a10kiloham/NicePillzViewZMK/boards/shields/nicepillz/custom_status_screen.c

/*
 * Nice Pillz nice!view status screen - ZMK glue.
 *
 * Portrait layout, header pins at the bottom:
 *
 *      [=====]  87%     battery gauge + percent, or "Charging" when on USB
 *      [ 63 /\/\_ ]    words per minute: history graph, one sample per 5 s
 *      (BT) 1 ok        output: bluetooth logo + profile numeral, or a USB symbol
 *   (1)(2)(3)(4)(5)     active layer
 *     [Caps Lock]       HID lock indicators
 *    Ctrl Alt Shift     held modifier keys, and the Program key
 *      Win Prgm
 *
 * Everything is drawn upright into a 68x160 canvas by view_draw.c, then
 * rotated into the panel's native 160x68 buffer. All LVGL work happens on
 * the ZMK display work queue.
 *
 * With CONFIG_NICEPILLZ_DISPLAY_LANDSCAPE the same elements are laid out for
 * 160x68, drawn into the panel buffer and turned 180 degrees (header pins on the right).
 *
 * SPDX-License-Identifier: MIT
 */
#include <zephyr/kernel.h>
#include <string.h>
#include <lvgl.h>

#include <zmk/display.h>
#include <zmk/display/status_screen.h>
#include <zmk/event_manager.h>
#include <zmk/events/battery_state_changed.h>
#include <zmk/events/usb_conn_state_changed.h>
#include <zmk/events/ble_active_profile_changed.h>
#include <zmk/events/endpoint_changed.h>
#include <zmk/events/layer_state_changed.h>
#include <zmk/events/hid_indicators_changed.h>
#include <zmk/events/keycode_state_changed.h>
#include <dt-bindings/zmk/hid_usage.h>
#include <dt-bindings/zmk/hid_usage_pages.h>
#include <zmk/hid.h>
#include <zmk/battery.h>
#include <zmk/usb.h>
#include <zmk/ble.h>
#include <zmk/endpoints.h>
#include <zmk/keymap.h>
#include <zmk/hid_indicators.h>
#include <zmk/wpm.h>

#include "view_draw.h"

/* HID boot keyboard output report bits */
#define HID_LED_NUM_LOCK BIT(0)
#define HID_LED_CAPS_LOCK BIT(1)
#define HID_LED_SCROLL_LOCK BIT(2)

#if !IS_ENABLED(CONFIG_NICEPILLZ_DISPLAY_LANDSCAPE)
static lv_color_t upright_buf[NPV_W * NPV_H];
static lv_obj_t *upright_canvas;
#endif
static lv_color_t panel_buf[NPV_PANEL_W * NPV_PANEL_H];
static lv_obj_t *panel_canvas;

static struct npv_state state;
static K_MUTEX_DEFINE(state_lock);
static int64_t last_wpm_update;

/* Modifier keys currently down, one bit per HID usage Left Ctrl (0xE0) .. Right GUI (0xE7).
 * ZMK never raises zmk_modifiers_state_changed, so this is tracked from the keycode events. */
static uint8_t held_mod_keys;

static uint8_t mod_bits(uint8_t keys) {
    uint8_t m = 0;
    if (keys & 0x11) {
        m |= NPV_MOD_CTRL;
    }
    if (keys & 0x22) {
        m |= NPV_MOD_SHIFT;
    }
    if (keys & 0x44) {
        m |= NPV_MOD_ALT;
    }
    if (keys & 0x88) {
        m |= NPV_MOD_GUI;
    }
    return m;
}

static void capture_zmk_state(struct npv_state *s) {
    s->battery = zmk_battery_state_of_charge();
    s->charging = zmk_usb_is_powered();

    struct zmk_endpoint_instance ep = zmk_endpoints_selected();
    s->transport = (ep.transport == ZMK_TRANSPORT_USB) ? NPV_TRANSPORT_USB : NPV_TRANSPORT_BLE;
    s->ble_profile = zmk_ble_active_profile_index();
    s->ble_connected = zmk_ble_active_profile_is_connected();
    s->ble_open = zmk_ble_active_profile_is_open();

    s->layer = zmk_keymap_highest_layer_active();

    zmk_hid_indicators_t ind = zmk_hid_indicators_get_current_profile();
    s->num_lock = ind & HID_LED_NUM_LOCK;
    s->caps_lock = ind & HID_LED_CAPS_LOCK;
    s->scroll_lock = ind & HID_LED_SCROLL_LOCK;

    s->mods = mod_bits(held_mod_keys);
    if (zmk_keymap_layer_active(CONFIG_NICEPILLZ_PROGRAM_LAYER)) {
        s->mods |= NPV_MOD_PRGM;
    }

    s->inverted = IS_ENABLED(CONFIG_NICEPILLZ_DISPLAY_INVERTED);
}

/* Runs on the display work queue. */
static void redraw_handler(struct k_work *work) {
    struct npv_state snapshot;
    k_mutex_lock(&state_lock, K_FOREVER);
    snapshot = state;
    k_mutex_unlock(&state_lock);

#if IS_ENABLED(CONFIG_NICEPILLZ_DISPLAY_LANDSCAPE)
    npv_draw_landscape(panel_canvas, &snapshot);
    npv_flip(panel_buf);
#else
    npv_draw(upright_canvas, &snapshot);
    npv_rotate(upright_buf, panel_buf);
#endif
    lv_obj_invalidate(panel_canvas);
}

K_WORK_DEFINE(redraw_work, redraw_handler);

/* Any ZMK state event: re-read everything and redraw. */
static int zmk_event_listener(const zmk_event_t *eh) {
    const struct zmk_keycode_state_changed *kc = as_zmk_keycode_state_changed(eh);
    if (kc) {
        if (kc->usage_page != HID_USAGE_KEY || kc->keycode < HID_USAGE_KEY_KEYBOARD_LEFTCONTROL ||
            kc->keycode > HID_USAGE_KEY_KEYBOARD_RIGHT_GUI) {
            return ZMK_EV_EVENT_BUBBLE; /* not a modifier key, nothing to show */
        }
        WRITE_BIT(held_mod_keys, kc->keycode - HID_USAGE_KEY_KEYBOARD_LEFTCONTROL, kc->state);
    }

    k_mutex_lock(&state_lock, K_FOREVER);
    capture_zmk_state(&state);
    k_mutex_unlock(&state_lock);
    k_work_submit_to_queue(zmk_display_work_q(), &redraw_work);
    return ZMK_EV_EVENT_BUBBLE;
}

ZMK_LISTENER(npv_listener, zmk_event_listener);
ZMK_SUBSCRIPTION(npv_listener, zmk_battery_state_changed);
ZMK_SUBSCRIPTION(npv_listener, zmk_usb_conn_state_changed);
ZMK_SUBSCRIPTION(npv_listener, zmk_ble_active_profile_changed);
ZMK_SUBSCRIPTION(npv_listener, zmk_endpoint_changed);
ZMK_SUBSCRIPTION(npv_listener, zmk_layer_state_changed);
ZMK_SUBSCRIPTION(npv_listener, zmk_hid_indicators_changed);
ZMK_SUBSCRIPTION(npv_listener, zmk_keycode_state_changed);

/* Once a second on the display queue: every CONFIG_NICEPILLZ_WPM_INTERVAL_MS push the current
 * WPM into the history and redraw the graph. */
static void tick_handler(struct k_work *work) {
    int64_t now = k_uptime_get();
    if ((now - last_wpm_update) < CONFIG_NICEPILLZ_WPM_INTERVAL_MS) {
        return;
    }
    last_wpm_update = now;

    k_mutex_lock(&state_lock, K_FOREVER);
    int wpm = zmk_wpm_get_state();
    state.wpm = wpm;
    memmove(&state.wpm_hist[0], &state.wpm_hist[1], NPV_WPM_POINTS - 1);
    state.wpm_hist[NPV_WPM_POINTS - 1] = wpm > 255 ? 255 : wpm;
    k_mutex_unlock(&state_lock);

    redraw_handler(NULL);
}

K_WORK_DEFINE(tick_work, tick_handler);

static void tick_timer_cb(struct k_timer *timer) {
    k_work_submit_to_queue(zmk_display_work_q(), &tick_work);
}

K_TIMER_DEFINE(tick_timer, tick_timer_cb, NULL);

lv_obj_t *zmk_display_status_screen(void) {
    lv_obj_t *screen = lv_obj_create(NULL);

    panel_canvas = lv_canvas_create(screen);
    lv_canvas_set_buffer(panel_canvas, panel_buf, NPV_PANEL_W, NPV_PANEL_H, LV_IMG_CF_TRUE_COLOR);
    lv_obj_align(panel_canvas, LV_ALIGN_TOP_LEFT, 0, 0);

#if !IS_ENABLED(CONFIG_NICEPILLZ_DISPLAY_LANDSCAPE)
    /* scratch canvas for the upright drawing, never shown directly */
    upright_canvas = lv_canvas_create(screen);
    lv_canvas_set_buffer(upright_canvas, upright_buf, NPV_W, NPV_H, LV_IMG_CF_TRUE_COLOR);
    lv_obj_add_flag(upright_canvas, LV_OBJ_FLAG_HIDDEN);
#endif

    k_mutex_lock(&state_lock, K_FOREVER);
    capture_zmk_state(&state);
    state.wpm = zmk_wpm_get_state();
    k_mutex_unlock(&state_lock);
    last_wpm_update = k_uptime_get();

    redraw_handler(NULL);
    k_timer_start(&tick_timer, K_SECONDS(1), K_SECONDS(1));

    return screen;
}
